jamesSaporito/FreeformClock/kicad/FreeformClock/FreeformClock.kicad_sch

## KiCad design kicad/FreeformClock/FreeformClock.kicad_sch (2026-02-03)

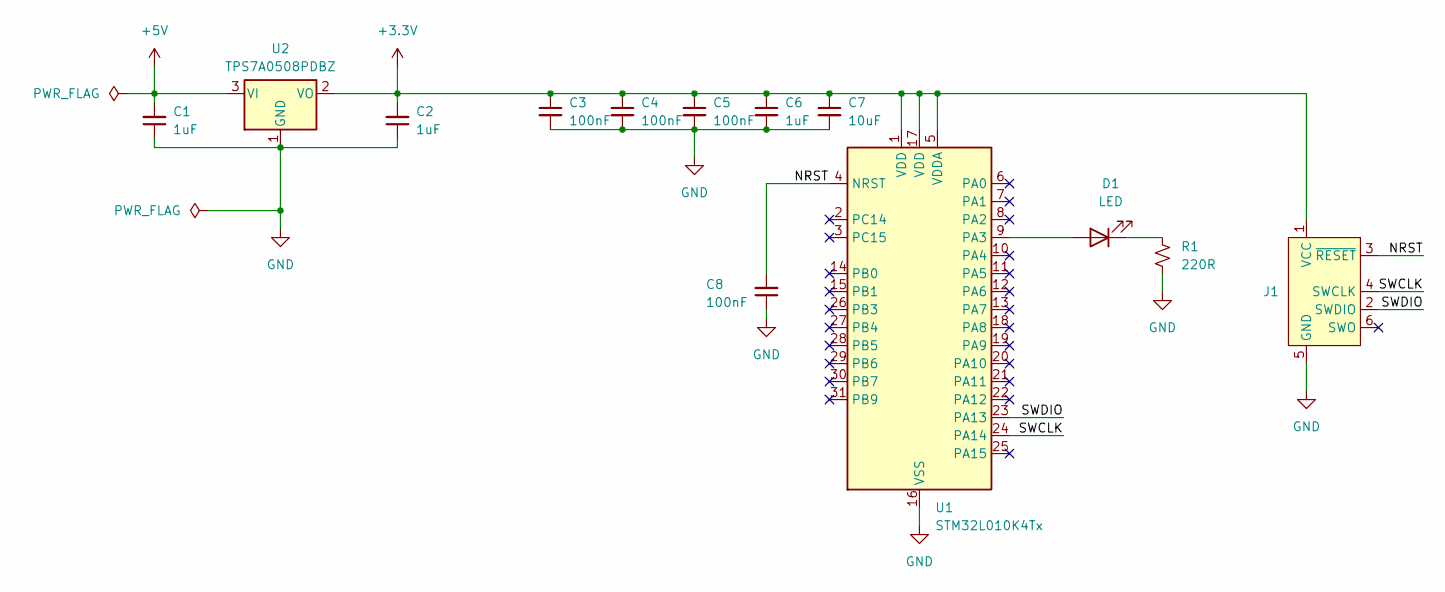
[picture p4: schematic FreeformClock.kicad_sch]

Parts:
C1, C2, C6: 1uF
C3, C4: 100nF; JLCPCB # C1525
C5, C8: 100nF
C7: 10uF
D1: LED
J1: Conn_ARM_SWD_TagConnect_TC2030; Tag-Connect_TC2030-IDC-FP_2x03_P1.27mm_Vertical
R1: 220R
U1: STM32L010K4Tx; LQFP-32_7x7mm_P0.8mm
U2: TPS7A0508PDBZ; SOT-23

Connections:
+3.3V: C2.2, C3.1, C4.1, C5.1, C6.1, C7.1, J1.1 (VCC), U1.1 (VDD), U1.5 (VDDA), U1.17 (VDD), U2.2 (VO)
+5V: C1.2, U2.3 (VI)
GND: C1.1, C2.1, C3.2, C4.2, C5.2, C6.2, C7.2, C8.1, J1.5 (GND), R1.2, U1.16 (VSS), U1.32 (VSS), U2.1 (GND)
NRST: C8.2, J1.3 (~RESET), U1.4 (NRST)
unnamed: D1.1 (K), R1.1
unnamed: D1.2 (A), U1.9 (PA3)
SWCLK: J1.4 (SWCLK), U1.24 (PA14)
SWDIO: J1.2 (SWDIO), U1.23 (PA13)
